docteurzoidberg/zillo-mini-devkit/stl/3D_RGB_DreamLight/images/4b9f2a6351e01b71ba1de5f23d602e25_preview_featured.jpg

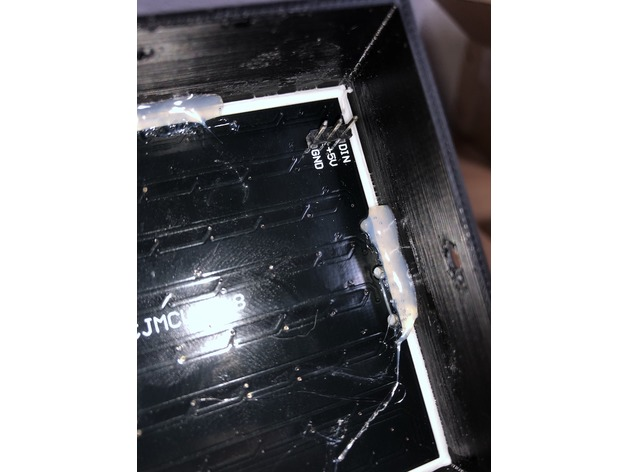
stl/3D_RGB_DreamLight/images/4b9f2a6351e01b71ba1de5f23d602e25_preview_featured.jpg
