docteurzoidberg/zillo-mini-devkit/stl/3D_RGB_DreamLight/images/50ee6cd8ead8aef76037b15bb34f3d4b_preview_featured.jpg

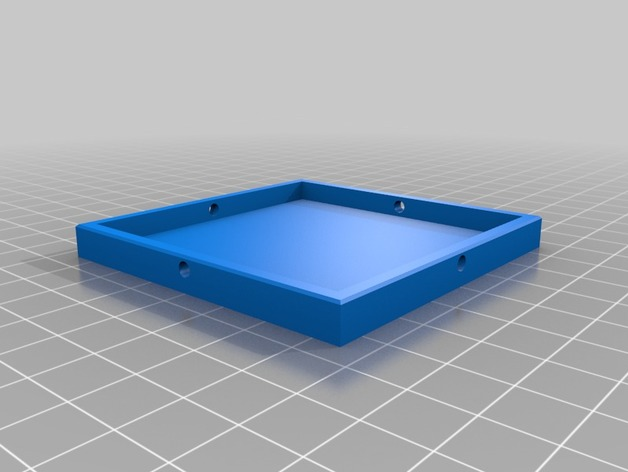
stl/3D_RGB_DreamLight/images/50ee6cd8ead8aef76037b15bb34f3d4b_preview_featured.jpg
