docteurzoidberg/zillo-mini-devkit/stl/3D_RGB_DreamLight/images/101130764b41f5a51d9ef1fc33212d11_preview_featured.jpg

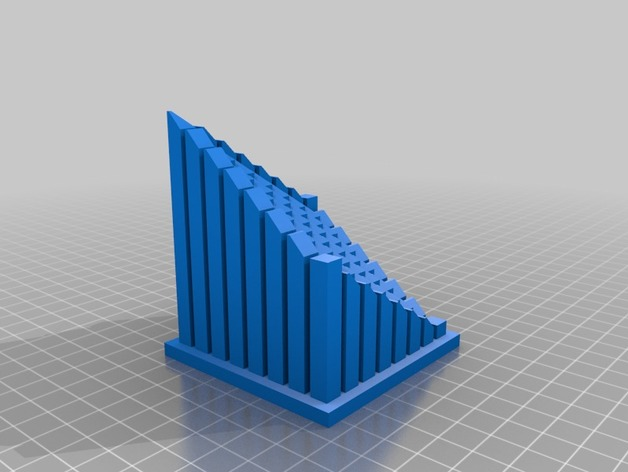
stl/3D_RGB_DreamLight/images/101130764b41f5a51d9ef1fc33212d11_preview_featured.jpg
