docteurzoidberg/zillo-mini-devkit/stl/3D_RGB_DreamLight/images/fb40c8f0eb7c7081e2b8a7114e15738c_preview_featured.jpg

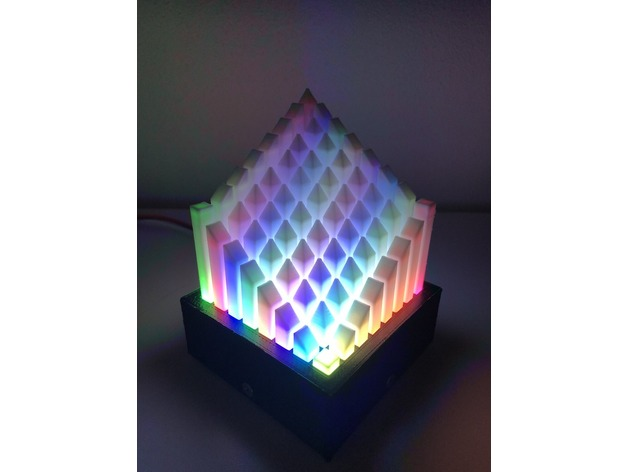
stl/3D_RGB_DreamLight/images/fb40c8f0eb7c7081e2b8a7114e15738c_preview_featured.jpg
